captmicr0/Canon-Pixma-IP6600D/parts/automatic slot feeder/reference pictures/canon_pixma_ip6600d_1.png

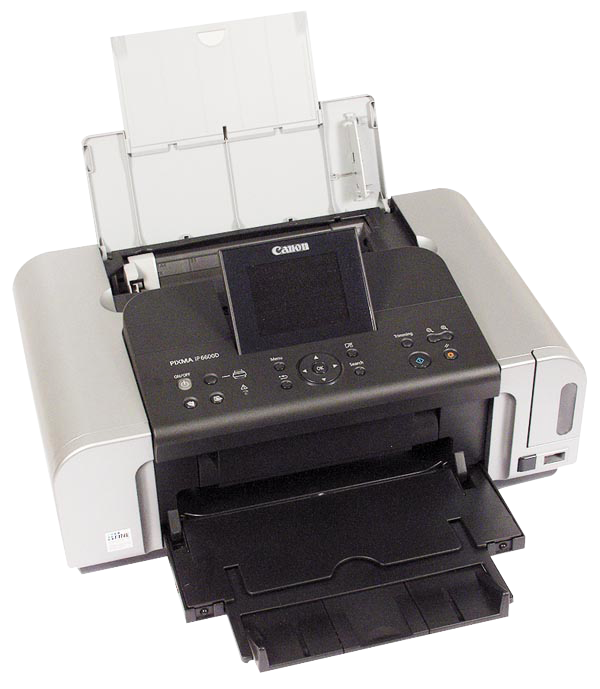
parts/automatic slot feeder/reference pictures/canon_pixma_ip6600d_1.png
