captmicr0/Canon-Pixma-IP6600D/parts/automatic slot feeder/reference pictures/front.webp

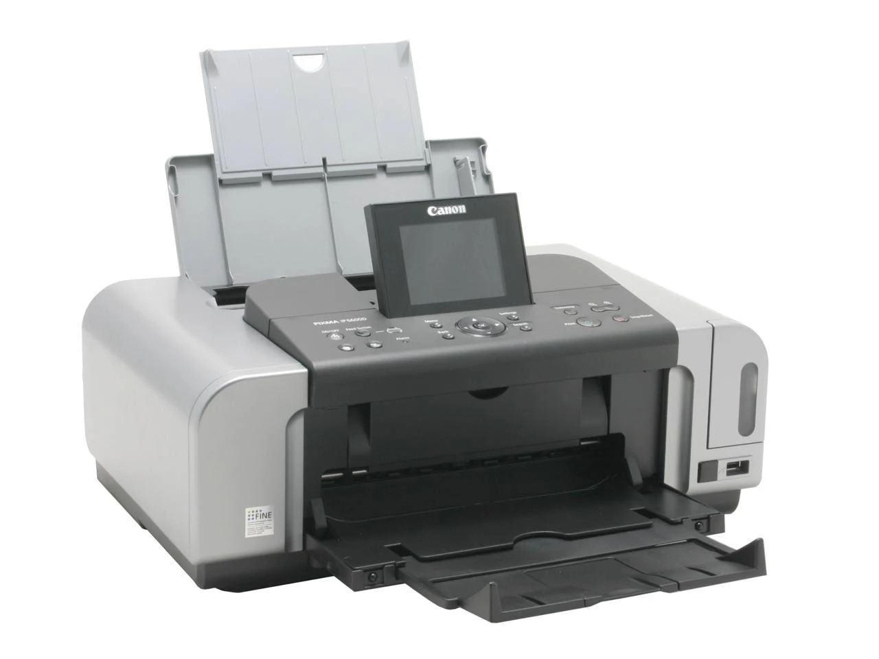
parts/automatic slot feeder/reference pictures/front.webp
