captmicr0/Canon-Pixma-IP6600D/parts/sd card door/IMG_1973.jpeg

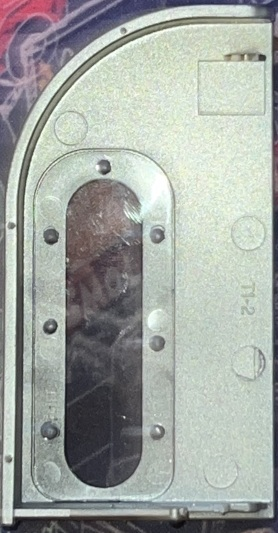
parts/sd card door/IMG_1973.jpeg
