captmicr0/Canon-Pixma-IP6600D/parts/automatic slot feeder/reference pictures/epson-vs-brother-printers-which-is-better_800x.webp

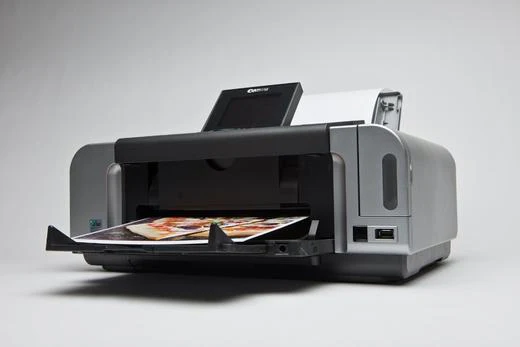
parts/automatic slot feeder/reference pictures/epson-vs-brother-printers-which-is-better_800x.webp
